7FM/ReflowOvenControl/include/notes.hpp

#pragma once

#include <avr/pgmspace.h>

#define _NOTE_B0 31
#define _NOTE_C1 33
#define _NOTE_CS1 35
#define _NOTE_D1 37
#define _NOTE_DS1 39
#define _NOTE_E1 41
#define _NOTE_F1 44
#define _NOTE_FS1 46
#define _NOTE_G1 49
#define _NOTE_GS1 52
#define _NOTE_A1 55
#define _NOTE_AS1 58
#define _NOTE_B1 62
#define _NOTE_C2 65
#define _NOTE_CS2 69
#define _NOTE_D2 73
#define _NOTE_DS2 78
#define _NOTE_E2 82
#define _NOTE_F2 87
#define _NOTE_FS2 93
#define _NOTE_G2 98
#define _NOTE_GS2 104
#define _NOTE_A2 110
#define _NOTE_AS2 117
#define _NOTE_B2 123
#define _NOTE_C3 131
#define _NOTE_CS3 139
#define _NOTE_D3 147
#define _NOTE_DS3 156
#define _NOTE_E3 165
#define _NOTE_F3 175
#define _NOTE_FS3 185
#define _NOTE_G3 196
#define _NOTE_GS3 208
#define _NOTE_A3 220
#define _NOTE_AS3 233
#define _NOTE_B3 247
#define _NOTE_C4 262
#define _NOTE_CS4 277
#define _NOTE_D4 294
#define _NOTE_DS4 311
#define _NOTE_E4 330
#define _NOTE_F4 349
#define _NOTE_FS4 370
#define _NOTE_G4 392
#define _NOTE_GS4 415
#define _NOTE_A4 440
#define _NOTE_AS4 466
#define _NOTE_B4 494
#define _NOTE_C5 523
#define _NOTE_CS5 554
#define _NOTE_D5 587
#define _NOTE_DS5 622
#define _NOTE_E5 659
#define _NOTE_F5 698
#define _NOTE_FS5 740
#define _NOTE_G5 784
#define _NOTE_GS5 831
#define _NOTE_A5 880
#define _NOTE_AS5 932
#define _NOTE_B5 988
#define _NOTE_C6 1047
#define _NOTE_CS6 1109
#define _NOTE_D6 1175
#define _NOTE_DS6 1245
#define _NOTE_E6 1319
#define _NOTE_F6 1397
#define _NOTE_FS6 1480
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
    NOTE_AS6,
    NOTE_B6,
    NOTE_C7,
    NOTE_CS7,
    NOTE_D7,
    NOTE_DS7,
    NOTE_E7,
    NOTE_F7,
    NOTE_FS7,
    NOTE_G7,
    NOTE_GS7,
    NOTE_A7,
    NOTE_AS7,
    NOTE_B7,
    NOTE_C8,
    NOTE_CS8,
    NOTE_D8,
    NOTE_DS8,
    REST,
    TUNE_END,
    TUNE_SET_NOTE_LENGTH,
};
