7FM/ReflowOvenControl/src/graphicstest.hpp

#if defined(DEBUG) && defined(BENCHMARK)
void printnice(int32_t v) {
    char str[32] = {0};
    sprintf(str, "%lu", v);
    for (char *p = (str + strlen(str)) - 3; p > str; p -= 3) {
        memmove(p + 1, p, strlen(p) + 1);
        *p = ',';
    }
    while (strlen(str) < 10) {
        memmove(str + 1, str, strlen(str) + 1);
        *str = ' ';
    }
    tft.print(str);
}

static inline uint32_t micros_start() __attribute__((always_inline));
static inline uint32_t micros_start() {
    uint8_t oms = millis();
    while ((uint8_t)millis() == oms)
        ;
    return micros();
}

uint32_t testHaD() {
    // pseudo-code for cheesy RLE
    // start with color1
    // while more input data remaining
    // 	count =  0nnnnnnn = 1 byte or 1nnnnnnn nnnnnnnn 2 bytes (0 - 32767)
    // 	repeat color count times
    // 	toggle color1/color2
    static const uint8_t HaD_240x320[] PROGMEM = {
        0xb9,
        0x50,
        0x0e,
        0x80,
        0x93,
        0x0e,
        0x41,
        0x11,
        0x80,
        0x8d,
        0x11,
        0x42,
        0x12,
        0x80,
        0x89,
        0x12,
        0x45,
        0x12,
        0x80,
        0x85,
        0x12,
        0x48,
        0x12,
        0x80,
        0x83,
        0x12,
        0x4a,
        0x13,
        0x7f,
        0x13,
        0x4c,
        0x13,
        0x7d,
        0x13,
        0x4e,
        0x13,
        0x7b,
        0x13,
        0x50,
        0x13,
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
    };

    tft.fillScreen(ST7735_BLACK);

    uint32_t start = micros_start();

    for (int i = 0; i < 0x10; i++) {
        tft.setAddrWindow(0, 0, MIN(240, tft.width()), MIN(320, tft.height()));

        uint16_t cnt = 0;
        uint16_t color = tft.color565((i << 4) | i, (i << 4) | i, (i << 4) | i);
        uint16_t curcolor = 0;

        const uint8_t *cmp = &HaD_240x320[0];

        while (cmp < &HaD_240x320[sizeof(HaD_240x320)]) {
            cnt = pgm_read_byte(cmp++);
            if (cnt & 0x80)
                cnt = ((cnt & 0x7f) << 8) | pgm_read_byte(cmp++);

            cnt = MIN(cnt, (uint16_t)tft.width());

#if defined(_PDQ_ST7735H_)
            tft.pushColor(curcolor, cnt); // PDQ_GFX has count
#else
            while (cnt--)
                tft.pushColor(curcolor); // Adafruit needs a loop
#endif
            curcolor ^= color;
        }
    }

    uint32_t t = micros() - start;

    tft.setTextColor(ST7735_YELLOW);
    tft.setTextSize(1);
    tft.setCursor(24, 285);
    tft.print(F("http://hackaday.io/"));
    tft.setCursor(100, 306);
    tft.print(F("Xark"));

    delay(3 * 1000L);

    return t;
}

uint32_t testFillScreen() {
    uint32_t start = micros_start();

    for (uint8_t i = 0; i < 12; i++) {
        tft.fillScreen(ST7735_BLACK);
        tft.fillScreen(ST7735_WHITE);
        tft.fillScreen(ST7735_RED);
        tft.fillScreen(ST7735_GREEN);
        tft.fillScreen(ST7735_BLUE);
    }

    return micros() - start;
}

uint32_t testText() {
    tft.fillScreen(ST7735_BLACK);
    uint32_t start = micros_start();
    tft.setCursor(0, 0);
    tft.setTextColor(ST7735_WHITE);
    tft.setTextSize(1);
    tft.println(F("Hello World!"));
    tft.setTextSize(2);
    tft.setTextColor(tft.color565(0xff, 0x00, 0x00));
    tft.print(F("RED "));
    tft.setTextColor(tft.color565(0x00, 0xff, 0x00));
    tft.print(F("GREEN "));
    tft.setTextColor(tft.color565(0x00, 0x00, 0xff));
    tft.println(F("BLUE"));
    tft.setTextColor(ST7735_YELLOW);
    tft.setTextSize(2);
    tft.println(1234.56);
    tft.setTextColor(ST7735_RED);
    tft.setTextSize(3);
    tft.println(0xDEADBEEF, HEX);
    tft.println();
    tft.setTextColor(ST7735_GREEN);
    tft.setTextSize(5);
    tft.println(F("Groop"));
    tft.setTextSize(2);
    tft.println(F("I implore thee,"));
    tft.setTextSize(1);
    tft.println(F("my foonting turlingdromes."));
    tft.println(F("And hooptiously drangle me"));
    tft.println(F("with crinkly bindlewurdles,"));
    tft.println(F("Or I will rend thee"));
    tft.println(F("in the gobberwarts"));
    tft.println(F("with my blurglecruncheon,"));
    tft.println(F("see if I don't!"));
    tft.println(F(""));
    tft.println(F(""));
    tft.setTextColor(ST7735_WHITE);
    tft.setTextSize(1);
    //tft.setFont(&FreeSerif12pt7b);
    tft.print(F("FreeSerif12pt font\n"));
    //tft.setFont(&FreeSans12pt7b);
    int16_t x1, y1;
    uint16_t w, h;
    tft.getTextBounds(F("FreeSans12pt7b\ngfxFont example."), tft.getCursorX(), tft.getCursorY(), &x1, &y1, &w, &h);
    tft.drawRect(x1, y1, w, h, ST7735_BLUE);
    tft.print(F("FreeSans12pt7b\nglxFont example.\n"));
    //tft.setFont(NULL);

    uint32_t t = micros() - start;
    delay(5000);
    return t;
}

uint32_t testPixels() {
    int32_t w = tft.width();
    int32_t h = tft.height();

    uint32_t start = micros_start();

    for (uint16_t y = 0; y < h; y++) {
        for (uint16_t x = 0; x < w; x++) {
            tft.drawPixel(x, y, tft.color565(x << 3, y << 3, x * y));
        }
    }

    return micros() - start;
}

uint32_t testLines(uint16_t color) {
    uint32_t start, t;
    int32_t x1, y1, x2, y2;
    int32_t w = tft.width();
    int32_t h = tft.height();

    tft.fillScreen(ST7735_BLACK);

    x1 = y1 = 0;
    y2 = h - 1;

    start = micros_start();

    for (x2 = 0; x2 < w; x2 += 6) {
        tft.drawLine(x1, y1, x2, y2, color);
    }

    x2 = w - 1;

    for (y2 = 0; y2 < h; y2 += 6) {
        tft.drawLine(x1, y1, x2, y2, color);
    }

    t = micros() - start; // fillScreen doesn't count against timing

    delay(5000);
    tft.fillScreen(ST7735_BLACK);

    x1 = w - 1;
    y1 = 0;
    y2 = h - 1;

    start = micros_start();

    for (x2 = 0; x2 < w; x2 += 6) {
        tft.drawLine(x1, y1, x2, y2, color);
    }

    x2 = 0;
    for (y2 = 0; y2 < h; y2 += 6) {
        tft.drawLine(x1, y1, x2, y2, color);
    }

    t += micros() - start;

    delay(5000);
    tft.fillScreen(ST7735_BLACK);

    x1 = 0;
    y1 = h - 1;
    y2 = 0;

    start = micros_start();

    for (x2 = 0; x2 < w; x2 += 6) {
        tft.drawLine(x1, y1, x2, y2, color);
    }
    x2 = w - 1;
    for (y2 = 0; y2 < h; y2 += 6) {
        tft.drawLine(x1, y1, x2, y2, color);
    }
    t += micros() - start;

    delay(5000);
    tft.fillScreen(ST7735_BLACK);

    x1 = w - 1;
    y1 = h - 1;
    y2 = 0;

    start = micros_start();

    for (x2 = 0; x2 < w; x2 += 6) {
        tft.drawLine(x1, y1, x2, y2, color);
    }

    x2 = 0;
    for (y2 = 0; y2 < h; y2 += 6) {
        tft.drawLine(x1, y1, x2, y2, color);
    }

    t += micros() - start;

    return t;
}

uint32_t testFastLines(uint16_t color1, uint16_t color2) {
    uint32_t start;
    int32_t x, y;
    int32_t w = tft.width();
    int32_t h = tft.height();

    tft.fillScreen(ST7735_BLACK);

    start = micros_start();

    for (y = 0; y < h; y += 5)
        tft.drawFastHLine(0, y, w, color1);
    for (x = 0; x < w; x += 5)
        tft.drawFastVLine(x, 0, h, color2);

    return micros() - start;
}

uint32_t testRects(uint16_t color) {
    uint32_t start;
    int32_t n, i, i2;
    int32_t cx = tft.width() / 2;
    int32_t cy = tft.height() / 2;

    tft.fillScreen(ST7735_BLACK);
    n = min(tft.width(), tft.height());
    start = micros_start();
    for (i = 2; i < n; i += 6) {
        i2 = i / 2;
        tft.drawRect(cx - i2, cy - i2, i, i, color);
    }

    return micros() - start;
}

uint32_t testFilledRects(uint16_t color1, uint16_t color2) {
    uint32_t start, t = 0;
    int32_t n, i, i2;
    int32_t cx = tft.width() / 2 - 1;
    int32_t cy = tft.height() / 2 - 1;

    tft.fillScreen(ST7735_BLACK);
    n = min(tft.width(), tft.height());
    for (i = n; i > 0; i -= 6) {
        i2 = i / 2;

        start = micros_start();

        tft.fillRect(cx - i2, cy - i2, i, i, color1);

        t += micros() - start;

        // Outlines are not included in timing results
        tft.drawRect(cx - i2, cy - i2, i, i, color2);
    }

    return t;
}

uint32_t testFilledCircles(uint8_t radius, uint16_t color) {
    uint32_t start;
    int32_t x, y, w = tft.width(), h = tft.height(), r2 = radius * 2;

    tft.fillScreen(ST7735_BLACK);

    start = micros_start();

    for (x = radius; x < w; x += r2) {
        for (y = radius; y < h; y += r2) {
            tft.fillCircle(x, y, radius, color);
        }
    }

    return micros() - start;
}

uint32_t testCircles(uint8_t radius, uint16_t color) {
    uint32_t start;
    int32_t x, y, r2 = radius * 2;
    int32_t w = tft.width() + radius;
    int32_t h = tft.height() + radius;

    // Screen is not cleared for this one -- this is
    // intentional and does not affect the reported time.
    start = micros_start();

    for (x = 0; x < w; x += r2) {
        for (y = 0; y < h; y += r2) {
            tft.drawCircle(x, y, radius, color);
        }
    }

    return micros() - start;
}

uint32_t testTriangles() {
    uint32_t start;
    int32_t n, i;
    int32_t cx = tft.width() / 2 - 1;
    int32_t cy = tft.height() / 2 - 1;

    tft.fillScreen(ST7735_BLACK);
    n = min(cx, cy);

    start = micros_start();

    for (i = 0; i < n; i += 5) {
        tft.drawTriangle(
            cx, cy - i,     // peak
            cx - i, cy + i, // bottom left
            cx + i, cy + i, // bottom right
            tft.color565(0, 0, i));
    }

    return micros() - start;
}

uint32_t testFilledTriangles() {
    uint32_t start, t = 0;
    int32_t i;
    int32_t cx = tft.width() / 2 - 1;
    int32_t cy = tft.height() / 2 - 1;

    tft.fillScreen(ST7735_BLACK);

    start = micros_start();

    for (i = min(cx, cy); i > 10; i -= 5) {
        start = micros_start();
        tft.fillTriangle(cx, cy - i, cx - i, cy + i, cx + i, cy + i,
                         tft.color565(0, i, i));
        t += micros() - start;
        tft.drawTriangle(cx, cy - i, cx - i, cy + i, cx + i, cy + i,
                         tft.color565(i, i, 0));
    }

    return t;
}

uint32_t testRoundRects() {
    uint32_t start;
    int32_t w, i, i2;
    int32_t cx = tft.width() / 2 - 1;
    int32_t cy = tft.height() / 2 - 1;

    tft.fillScreen(ST7735_BLACK);

    w = min(tft.width(), tft.height());

    start = micros_start();

    for (i = 0; i < w; i += 6) {
        i2 = i / 2;
        tft.drawRoundRect(cx - i2, cy - i2, i, i, i / 8, tft.color565(i, 0, 0));
    }

    return micros() - start;
}

uint32_t testFilledRoundRects() {
    uint32_t start;
    int32_t i, i2;
    int32_t cx = tft.width() / 2 - 1;
    int32_t cy = tft.height() / 2 - 1;

    tft.fillScreen(ST7735_BLACK);

    start = micros_start();

    for (i = min(tft.width(), tft.height()); i > 20; i -= 6) {
        i2 = i / 2;
        tft.fillRoundRect(cx - i2, cy - i2, i, i, i / 8, tft.color565(0, i, 0));
    }

    return micros() - start;
}

// These are used to get information about static SRAM and flash memory sizes
extern "C" char __data_start[];    // start of SRAM data
extern "C" char _end[];            // end of SRAM data (used to check amount of SRAM this program's variables use)
extern "C" char __data_load_end[]; // end of FLASH (used to check amount of Flash this program's code and data uses)

void benchmark(void) {
    Serial.print(F(__DATE__ " " __TIME__ " - Flash=0x"));
    Serial.print((uint16_t)__data_load_end, HEX);
    Serial.print(F(" RAM=0x"));
    Serial.println((uint16_t)_end - (uint16_t)__data_start, HEX);
    Serial.println(F("Benchmark                Time (microseconds)"));

    uint32_t usecHaD = testHaD();
    Serial.print(F("HaD pushColor            "));
    Serial.println(usecHaD);
    delay(5000);
    
    uint32_t usecFillScreen = testFillScreen();
    Serial.print(F("Screen fill              "));
    Serial.println(usecFillScreen);
    delay(5000);

    uint32_t usecText = testText();
    Serial.print(F("Text                     "));
    Serial.println(usecText);
    delay(5000);

    uint32_t usecPixels = testPixels();
    Serial.print(F("Pixels                   "));
    Serial.println(usecPixels);
    delay(5000);

    uint32_t usecLines = testLines(ST7735_BLUE);
    Serial.print(F("Lines                    "));
    Serial.println(usecLines);
    delay(5000);

    uint32_t usecFastLines = testFastLines(ST7735_RED, ST7735_BLUE);
    Serial.print(F("Horiz/Vert Lines         "));
    Serial.println(usecFastLines);
    delay(5000);

    uint32_t usecRects = testRects(ST7735_GREEN);
    Serial.print(F("Rectangles (outline)     "));
    Serial.println(usecRects);
    delay(5000);

    uint32_t usecFilledRects = testFilledRects(ST7735_YELLOW, ST7735_MAGENTA);
    Serial.print(F("Rectangles (filled)      "));
    Serial.println(usecFilledRects);
    delay(5000);

    uint32_t usecFilledCircles = testFilledCircles(10, ST7735_MAGENTA);
    Serial.print(F("Circles (filled)         "));
    Serial.println(usecFilledCircles);
    delay(5000);

    uint32_t usecCircles = testCircles(10, ST7735_WHITE);
    Serial.print(F("Circles (outline)        "));
    Serial.println(usecCircles);
    delay(5000);

    uint32_t usecTriangles = testTriangles();
    Serial.print(F("Triangles (outline)      "));
    Serial.println(usecTriangles);
    delay(5000);
    uint32_t usecFilledTrangles = testFilledTriangles();
    Serial.print(F("Triangles (filled)       "));
    Serial.println(usecFilledTrangles);
    delay(5000);

    
    uint32_t usecRoundRects = testRoundRects();
    Serial.print(F("Rounded rects (outline)  "));
    Serial.println(usecRoundRects);
    delay(5000);

    uint32_t usedFilledRoundRects = testFilledRoundRects();
    Serial.print(F("Rounded rects (filled)   "));
    Serial.println(usedFilledRoundRects);
    delay(5000);

    Serial.println(F("Done!"));

    uint16_t c = 4;
    int8_t d = 1;
    for (int32_t i = 0; i < tft.height(); i++) {
        tft.drawFastHLine(0, i, tft.width(), c);
        c += d;
        if (c <= 4 || c >= 11)
            d = -d;
    }

    tft.setCursor(0, 0);
    tft.setTextColor(ST7735_MAGENTA);
    tft.setTextSize(1);

#if defined(_PDQ_ST7735H_)
    tft.println(F(" PDQ GFX+PDQ ST7735"));
#else
    tft.println(F(" Adafruit GFX+ST7735"));
#endif
    tft.setTextColor(ST7735_WHITE);
    tft.print(F("SPI LCD on 328p@16MHz"));
    tft.setTextColor(tft.color565(0x80, 0x80, 0x80));
    tft.print(F("Fl=0x"));
    tft.print((uint16_t)__data_load_end, HEX);
    tft.print(F(" RAM=0x"));
    tft.print((uint16_t)_end - (uint16_t)__data_start, HEX);
    tft.println();

    tft.setTextColor(ST7735_GREEN);
    tft.print(F("Benchmark        usec"));
    tft.setTextColor(ST7735_YELLOW);

    tft.setTextColor(ST7735_CYAN);
    tft.print(F("HaD psCol  "));
    tft.setTextColor(ST7735_YELLOW);
    tft.setTextSize(1);
    printnice(usecHaD);

    tft.setTextColor(ST7735_CYAN);
    tft.print(F("Fill       "));
    tft.setTextColor(ST7735_YELLOW);
    tft.setTextSize(1);
    printnice(usecFillScreen);

    tft.setTextColor(ST7735_CYAN);
    tft.print(F("Text       "));
    tft.setTextColor(ST7735_YELLOW);
    tft.setTextSize(1);
    printnice(usecText);

    tft.setTextColor(ST7735_CYAN);
    tft.print(F("Pixels     "));
    tft.setTextColor(ST7735_YELLOW);
    tft.setTextSize(1);
    printnice(usecPixels);

    tft.setTextColor(ST7735_CYAN);
    tft.print(F("Lines      "));
    tft.setTextColor(ST7735_YELLOW);
    printnice(usecLines);

    tft.setTextColor(ST7735_CYAN);
    tft.print(F("H/V Lines  "));
    tft.setTextColor(ST7735_YELLOW);
    printnice(usecFastLines);

    tft.setTextColor(ST7735_CYAN);
    tft.print(F("Rectangles "));
    tft.setTextColor(ST7735_YELLOW);
    printnice(usecRects);

    tft.setTextColor(ST7735_CYAN);
    tft.print(F("Rects-Fill "));
    tft.setTextColor(ST7735_YELLOW);
    printnice(usecFilledRects);

    tft.setTextColor(ST7735_CYAN);
    tft.print(F("Circles    "));
    tft.setTextColor(ST7735_YELLOW);
    printnice(usecCircles);

    tft.setTextColor(ST7735_CYAN);
    tft.print(F("CirclesFill"));
    tft.setTextColor(ST7735_YELLOW);
    printnice(usecFilledCircles);

    tft.setTextColor(ST7735_CYAN);
    tft.print(F("Triangles  "));
    tft.setTextColor(ST7735_YELLOW);
    printnice(usecTriangles);

    tft.setTextColor(ST7735_CYAN);
    tft.print(F("Tri-Fill   "));
    tft.setTextColor(ST7735_YELLOW);
    printnice(usecFilledTrangles);

    tft.setTextColor(ST7735_CYAN);
    tft.print(F("Rnd-Rects  "));
    tft.setTextColor(ST7735_YELLOW);
    printnice(usecRoundRects);

    tft.setTextColor(ST7735_CYAN);
    tft.print(F("RRects-Fill"));
    tft.setTextColor(ST7735_YELLOW);
    printnice(usedFilledRoundRects);

    tft.println();
    tft.setTextColor(ST7735_GREEN);
    tft.print(F("Benchmark Completed!"));

    delay(60 * 1000L);
}
#endif
